isomorphisms/programmers-keyboard/pictures of the keypads/several pastebins push pop see.png

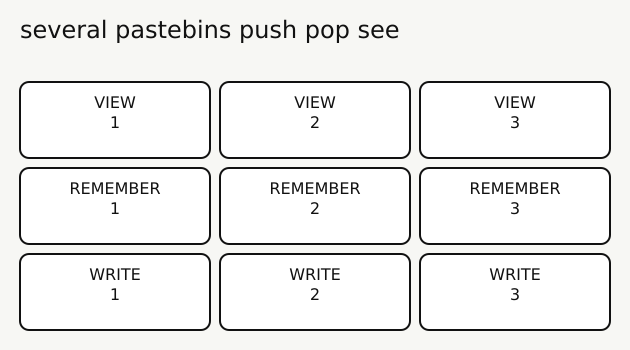
pictures of the keypads/several pastebins push pop see.png
